mantisrobot/lightsaber/SABER_V2/OFF_06S.h

const signed char saberOff[] = {
82,73,70,70,111,41,0,0,87,65,86,69,102,109,116,32,
16,0,0,0,1,0,1,0,-128,62,0,0,-128,62,0,0,
1,0,8,0,100,97,116,97,75,41,0,0,113,121,-123,109,
106,106,97,92,77,78,108,-125,-120,116,97,126,-105,-108,117,91,
104,-127,-117,-119,118,92,85,94,108,120,-123,120,110,107,95,95,
91,100,118,124,118,84,78,103,121,-121,108,89,113,-126,-111,-109,
122,-123,-106,124,125,-119,-116,-120,102,85,101,123,-123,-124,-121,-117,
-125,118,123,-112,-92,-96,-109,-116,-119,-103,-81,-72,-76,-98,-120,-117,
-103,-86,-75,-88,-121,-126,-118,-115,-93,-105,-128,119,110,-125,-102,-107,
-97,-120,119,-107,-112,-98,-69,-87,-115,125,127,-106,-97,-110,-117,-110,
-112,-125,121,-122,-107,-119,119,106,98,98,109,-127,-122,108,78,59,
74,95,98,111,109,91,101,97,87,100,102,89,92,110,100,90,
91,114,108,61,67,100,118,121,111,102,100,106,122,121,93,90,
114,112,86,77,100,94,71,91,103,107,-124,-122,-126,-123,-120,-106,
-112,-126,-126,126,-122,-104,-81,-75,-115,-128,-105,-95,-101,-100,-88,-78,
-90,-104,-81,-100,124,-106,-74,-107,111,126,-118,-88,-66,-111,103,124,
-82,-49,-68,-110,-110,-110,123,-126,-102,-106,126,115,111,126,-112,-116,
-121,119,99,93,98,110,-122,-118,100,81,104,107,104,107,125,-127,
85,70,112,-126,125,-101,-102,88,67,122,-99,-92,125,58,83,-107,
-98,-115,-126,117,-128,-107,-90,-82,-101,-105,117,93,121,-104,-75,-96,
118,112,118,-109,-82,-122,114,127,-116,-118,117,119,-116,-94,-83,-123,
103,122,-120,-111,-106,-83,120,68,119,-85,-66,-122,71,94,-94,-74,
111,75,94,124,-102,111,99,122,-113,-119,72,74,121,-108,-97,102,
58,100,-124,-99,127,72,78,93,99,88,103,113,80,79,89,87,
126,92,57,89,114,-108,94,52,82,-115,-108,66,69,122,-94,-125,
79,104,-126,-84,-106,93,90,-119,-100,107,98,-121,-90,-110,121,125,
-123,-111,-80,-88,-97,-78,-107,-102,-75,-86,-84,-104,-119,-83,-67,-54,
-96,-99,-62,-110,-102,-65,-86,-127,-119,-82,-105,-107,-78,-117,116,119,
-105,-95,-110,-102,127,121,-91,-69,120,83,-116,-83,118,101,124,122,
94,78,83,94,127,103,72,70,74,102,89,69,88,70,80,98,
-120,99,34,78,-103,-92,66,51,109,-116,-93,126,61,91,-124,-100,
-113,-128,127,91,98,-119,113,71,116,-91,-105,120,-109,-81,-102,121,
-110,-122,-125,-81,-97,-106,-80,-92,-116,-108,-101,-112,-91,-70,-109,-120,
-112,-102,-114,-89,-109,111,-114,-128,126,126,108,114,126,120,-127,-121,
-102,-123,97,124,105,110,-128,106,81,67,93,108,94,82,102,78,
78,102,72,63,89,95,66,58,67,76,105,-127,75,51,97,108,
106,-128,112,109,-121,110,113,-106,-107,117,-123,-103,-94,-94,-89,-78,
-107,-115,-107,-89,-68,-72,-109,-113,-81,-61,-48,-67,-74,-54,-38,-38,
-69,-91,-74,-43,-52,-73,-65,-65,-57,-56,-108,-125,-85,-77,-62,-72,
-109,-97,-116,116,-121,-108,106,79,96,101,106,85,91,104,91,82,
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

const uint32_t saberOffSize = sizeof(saberOff) / sizeof(saberOff[0]);
