mantisrobot/lightsaber/SABER_V2/ON_1S.h

const signed char saberOn[] = {
82,73,70,70,-98,63,0,0,87,65,86,69,102,109,116,32,
16,0,0,0,1,0,1,0,-128,62,0,0,-128,62,0,0,
1,0,8,0,100,97,116,97,18,63,0,0,127,126,127,127,
126,126,127,-128,127,127,-128,127,126,-128,127,126,127,126,126,127,
127,127,-128,127,127,127,-128,127,127,127,-128,-128,127,126,126,127,
126,-127,126,-128,127,127,-128,127,125,-127,-128,126,-127,-126,-126,124,
121,116,123,125,126,123,126,126,124,-128,-124,-125,126,-124,-123,-127,
-128,-122,-124,-127,-125,-122,-125,-123,-126,-128,127,-125,-128,126,122,125,
124,-114,-119,122,-126,106,98,86,126,125,-116,-125,123,-80,-107,87,
81,-93,126,88,102,120,-126,118,107,90,127,123,123,124,-100,-106,
127,-128,126,-121,-117,-72,-110,86,73,-71,-83,92,124,-127,124,115,
127,-120,-97,92,115,-77,90,86,-104,-105,-102,-113,79,-119,-72,120,
-119,-106,116,-123,-81,-124,119,114,-124,-75,125,81,-118,-102,96,-109,
-99,103,126,-110,121,109,108,124,-124,104,112,-106,114,88,-127,116,
127,-107,100,95,-85,122,89,-109,106,103,-104,-124,76,123,-88,115,
81,-102,-100,64,127,-89,119,117,117,108,-101,-119,96,118,-83,111,
55,-74,-108,50,-89,-75,61,118,-70,-127,76,-116,-112,90,-119,-83,
118,101,-92,-127,80,-82,-93,58,-87,-69,66,-117,-54,96,101,-64,
118,84,-76,-90,87,109,-81,-123,79,-82,-98,66,-98,-94,102,-115,
125,-127,-114,126,113,124,-104,116,109,118,-112,-128,80,-94,-101,42,
-128,-59,68,93,-93,121,105,90,-116,-109,62,-121,-102,99,-109,117,
75,-116,-102,92,113,-126,-104,121,75,-87,-96,62,-122,-47,86,83,
-73,-93,91,110,-80,122,97,-104,-76,117,78,-103,-72,110,98,-121,
-102,-121,-120,123,83,-99,-84,81,-110,-81,68,-117,-97,-110,120,71,
-84,-85,67,99,-67,-106,33,-75,-103,53,-84,104,-99,84,122,-118,
101,-91,64,-113,109,104,-87,105,116,-96,91,112,117,-128,-103,63,
-85,106,110,104,-105,-112,56,-49,96,125,109,-101,-107,79,-110,-94,
-126,80,-82,125,125,95,-109,-82,65,-121,-76,89,108,-65,83,-93,
114,93,-79,55,-69,126,122,-96,105,-100,80,-59,125,75,-54,75,
112,-118,-101,125,73,-65,113,90,126,-80,97,-125,-101,70,-78,110,
119,112,-94,113,85,-67,76,-126,-96,84,-84,123,75,-89,-128,121,
113,-58,87,118,-85,106,-124,98,-77,102,-120,108,-113,-127,106,-117,
-126,126,-120,-125,77,-66,116,88,-88,-118,70,-92,127,103,121,-111,
-114,83,-94,104,-89,94,-120,-80,68,-96,-122,76,-105,-67,84,125,
-90,73,-100,-126,110,-114,83,-72,59,-91,125,106,-96,83,-105,79,
-91,89,-94,125,89,-79,72,-116,-100,84,-101,96,127,-122,105,-116,
104,-96,81,-87,116,96,-106,95,-95,91,-108,-109,105,-89,91,-124,
-92,107,111,-120,114,-110,-106,71,-86,119,101,-112,122,-107,90,-103,
110,-118,-112,87,-81,102,122,-102,100,-83,107,-121,-111,-126,125,94,
-83,109,-104,85,-101,107,126,115,126,-86,58,-88,90,-91,82,124,
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

const uint32_t saberOnSize = sizeof(saberOn) / sizeof(saberOn[0]);
