mantisrobot/lightsaber/SABER_V2/hum_3sm.h

const signed char saberHum[]  = {
-45,-48,-45,-43,-45,-43,-45,-43,-45,-43,-45,-43,-45,-43,-45,-48,
-45,-48,-50,-50,-48,-50,-53,-50,-53,-56,-53,-56,-56,-58,-61,-58,
-61,-64,-66,-66,-69,-69,-71,-71,-74,-77,-79,-82,-84,-87,-92,-95,
-95,-100,-105,-110,-113,-118,-123,-128,122,120,114,109,104,102,94,91,
88,83,78,73,70,68,60,57,55,52,49,47,44,44,42,42,
39,39,36,39,36,34,36,37,34,36,34,36,34,36,37,39,
37,39,39,42,39,42,42,44,44,47,44,47,47,50,49,52,
49,52,55,52,55,57,55,57,57,60,57,60,62,62,65,65,
68,70,73,73,75,78,81,83,88,91,96,99,102,107,109,114,
120,122,-128,-123,-121,-116,-110,-105,-100,-97,-92,-90,-87,-79,-77,-74,
-69,-66,-66,-61,-58,-56,-53,-53,-50,-48,-48,-48,-45,-43,-45,-43,
-43,-40,-43,-40,-38,-37,-40,-37,-40,-43,-40,-40,-43,-40,-43,-45,
-45,-48,-45,-48,-50,-48,-50,-53,-50,-53,-56,-56,-58,-56,-58,-61,
-61,-63,-61,-61,-63,-63,-66,-69,-69,-71,-71,-71,-74,-76,-79,-82,
-84,-87,-89,-95,-100,-100,-102,-110,-113,-115,-121,-126,125,122,117,112,
107,104,99,94,91,86,83,75,73,70,65,62,60,57,55,49,
47,47,44,44,42,42,39,39,36,34,36,37,34,34,36,34,
36,34,36,34,36,39,39,37,39,42,42,44,44,47,44,47,
50,49,52,52,52,52,55,55,57,60,57,60,60,62,65,65,
68,70,70,73,76,78,81,83,86,91,94,96,102,104,109,112,
115,120,125,127,-123,-118,-113,-108,-105,-100,-95,-89,-87,-84,-79,-76,
-74,-69,-66,-66,-61,-61,-56,-53,-53,-50,-50,-48,-48,-45,-48,-45,
-43,-45,-43,-45,-43,-45,-43,-45,-43,-45,-48,-45,-48,-48,-48,-50,
-48,-50,-53,-50,-53,-56,-53,-56,-58,-56,-58,-61,-58,-61,-61,-63,
-66,-66,-69,-71,-71,-74,-76,-79,-82,-84,-87,-92,-95,-97,-102,-108,
-113,-115,-121,-126,125,122,117,112,107,102,99,91,88,86,81,78,
73,70,68,62,60,57,52,49,49,47,44,44,42,42,39,37,
36,34,36,34,36,34,34,37,34,36,34,36,34,36,37,39,
37,39,42,39,42,44,42,44,47,44,47,49,47,50,49,52,
52,55,52,55,57,55,57,60,57,60,60,62,65,65,68,70,
70,73,75,78,81,83,86,88,94,96,99,104,107,112,117,122,
125,-126,-121,-118,-113,-105,-102,-97,-92,-92,-87,-82,-79,-74,-71,-69,
-63,-61,-58,-56,-53,-53,-51,-48,-45,-48,-45,-43,-43,-40,-43,-40,
-43,-40,-37,-40,-37,-37,-40,-43,-40,-43,-40,-40,-43,-45,-43,-45,
-45,-48,-48,-48,-50,-53,-51,-56,-53,-56,-58,-56,-58,-61,-58,-61,
-61,-63,-63,-66,-63,-66,-66,-69,-71,-71,-77,-74,-79,-82,-82,-87,
-89,-95,-95,-97,-102,-108,-110,-116,-121,-126,-128,125,120,112,109,104,
99,94,88,86,81,78,75,70,65,62,57,55,52,50,47,47,
44,42,42,39,39,39,36,39,36,34,37,34,37,34,37,36,
39,37,39,42,39,39,42,44,42,44,44,47,49,47,50,52,
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

const uint32_t saberHumSize = sizeof(saberHum) / sizeof(saberHum[0]);
